TrojanPinata/DIY-Mic/modified stripboard.png

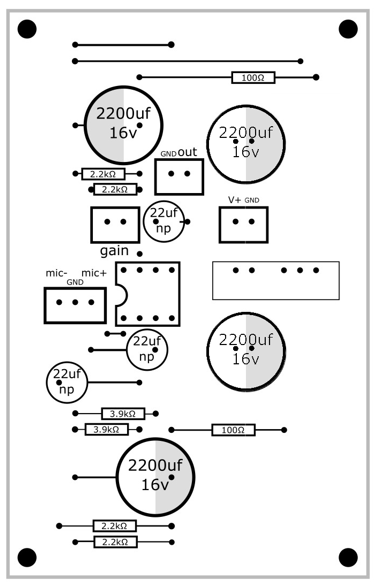
modified stripboard.png
