TrojanPinata/DIY-Mic/pics/Finished-Module (Small).jpg

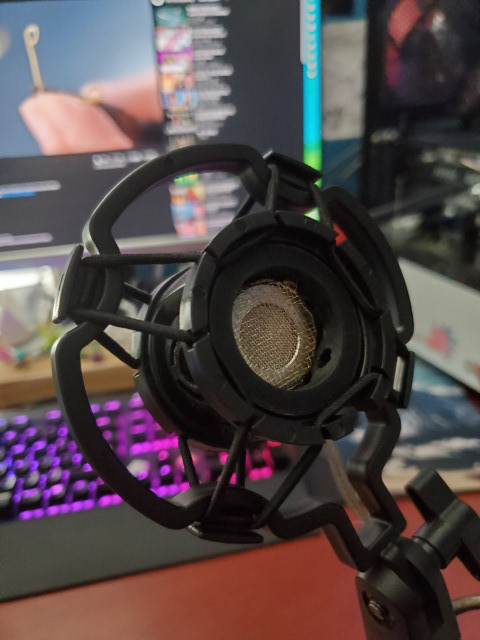
pics/Finished-Module (Small).jpg
